wtarreau/usb-current-limiter/output/pcb-600dpi.png

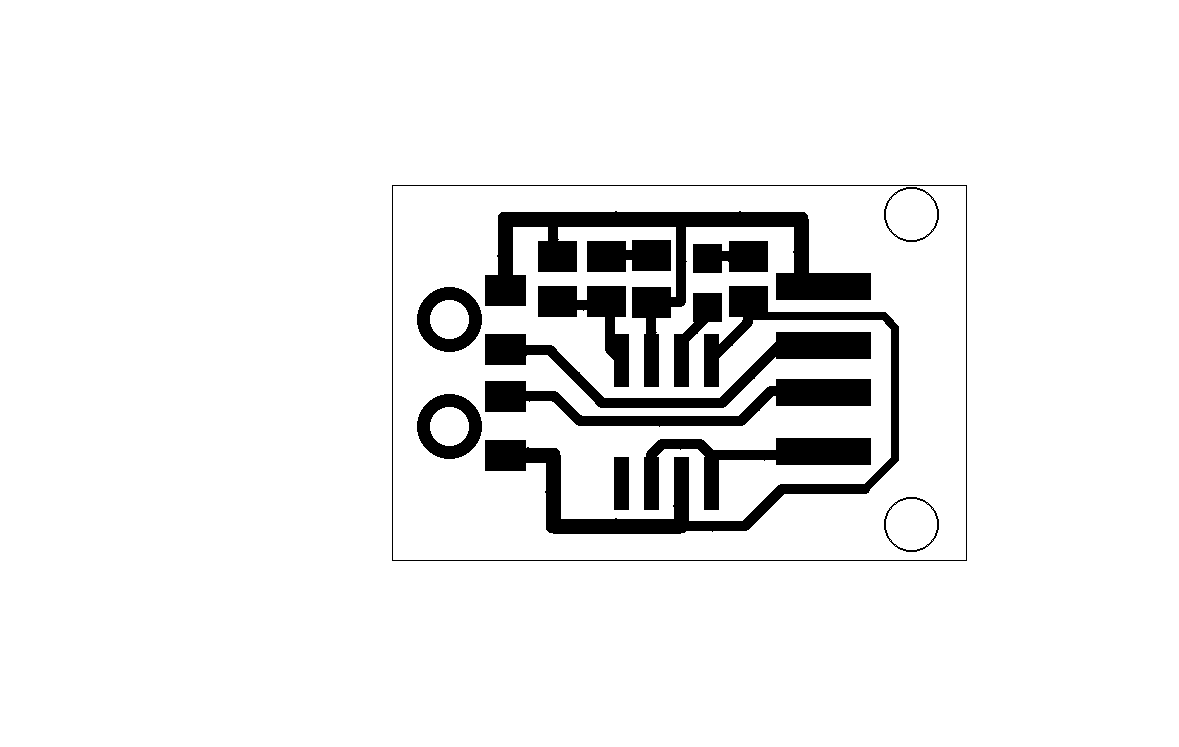
output/pcb-600dpi.png
