wtarreau/usb-current-limiter/output/pcb.png

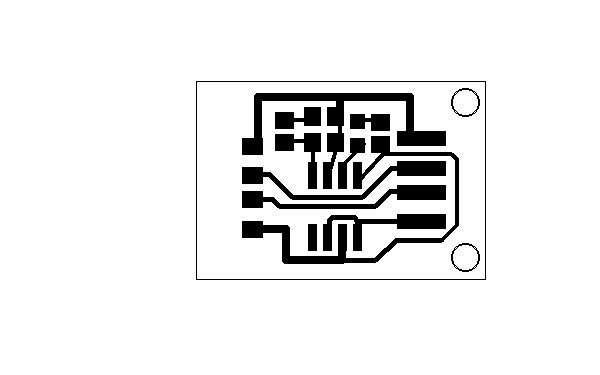
output/pcb.png
